JoaoMario109/ifsc-pi3-eletronic-load/docs/assets/eletronic-load.drawio.png

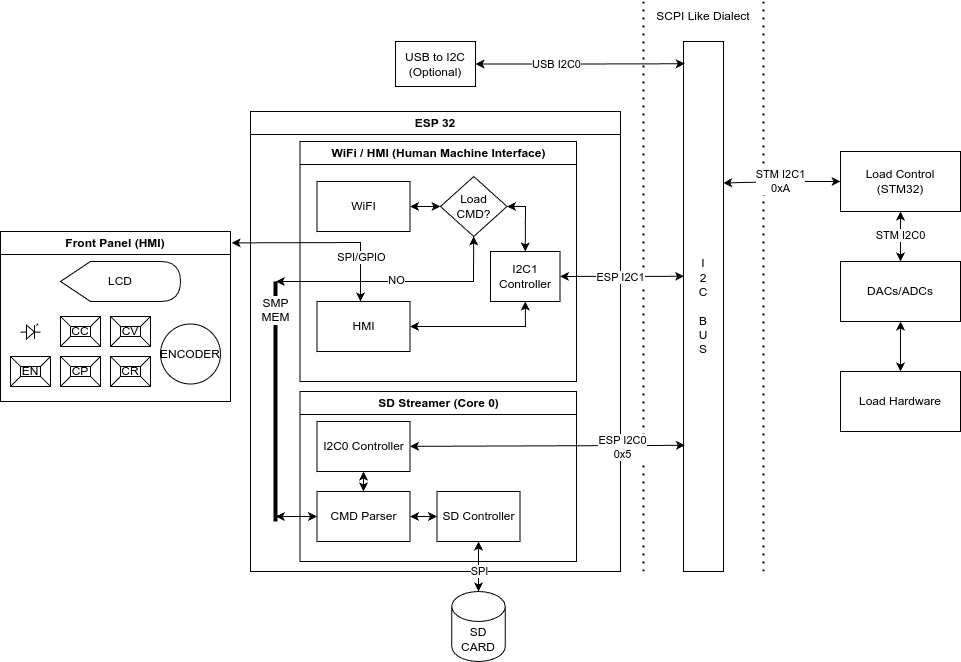
docs/assets/eletronic-load.drawio.png
