JoaoMario109/ifsc-pi3-eletronic-load/simulations/control/pid-hall.asc

C3: cap; 100n
C6: cap; 1n
D3: diode; LL4148
D4: diode; LL4148
D5: diode; LL4148
D6: diode; LL4148
DUT: voltage; PULSE(5 12 0 0p 0p 1m 2m)
Q1: npn
Q2: pnp; 2SB1375
Q3: npn
R1: res; 10
R2: res; 0.1
R3: res; 10
R4: res; 10
R5: res; 3.3k
R6: res; 3.3k
R7: res; 2.7k
R8: res; 3.3k
R9: res; 3.3k
R10: res; 720
R11: res; 1k
R13: res; 5k
R14: res; 3.30k
R15: res; 0.1
R16: res; 1k
U1: LM324_ST
U3: LM324_ST
U5: 
V1: voltage-; 12
V2: voltage; 1.65
V3: voltage-; PULSE(0 0.4 0 1p 1p 0.5m 1m)
V5: voltage-; 3.3
Named nets: vcc, 0, +3.3V, B2, B1, i_sensor, control_action, _control_action, setpoint
.tran 0 16m 2m startup
R10 -> reducing resistance increace velocity and ringing
C3 -> increase capacitance decrease rise time and increase ringing
C6 -> + capacitance = lower speed
