JoaoMario109/ifsc-pi3-eletronic-load/simulations/analog/voltage.asc

C1: cap; 1µ
C2: cap; 100n
C3: cap; 10n
C4: cap; 100n
D2: zener; BZX84B12VL
D3: zener; BZX84B12VL
D4: zener; PH_BZX585-B3V3
Q1: npn
R1: res; 10k
R2: res; 51k
R3: res; 10k
R4: res; 51k
R5: res; 50k
R6: res; 50k
R7: res; 1k
R8: res; 1k
R9: res; 1k
R10: res; 500
R11: res; 100
U2: LM324_ST
V1: voltage; 12
Vcm1: voltage; SINE(5 5 100 0 0 0); AC 50
Vcm: voltage; PULSE(0 10 0 0.01 0.01 0 0.02)
Vdut1: voltage; SINE(0 100 1 0 0 0 0); AC 100
Vdut: voltage; PULSE(0 100 0 1 1 0 2)
Vripple: voltage; SINE(0 6 1k)
Named nets: 0, Vcc, vout, Vdut-, Vdut+
;.ac dec 1k 1 10k
.tran 0 2 0
