JoaoMario109/ifsc-pi3-eletronic-load/firmware/load/Core/Inc/main.h

#define EXTERNAL_TRIGGER_OUT_Pin GPIO_PIN_13
#define EXTERNAL_TRIGGER_OUT_GPIO_Port GPIOC
#define EXTERNAL_TRIGGER_IN_Pin GPIO_PIN_14
#define EXTERNAL_TRIGGER_IN_GPIO_Port GPIOC
#define LED_RED_Pin GPIO_PIN_7
#define LED_RED_GPIO_Port GPIOA
#define LED_GREEN_Pin GPIO_PIN_0
#define LED_GREEN_GPIO_Port GPIOB
#define ADC_ALERT_Pin GPIO_PIN_1
#define ADC_ALERT_GPIO_Port GPIOB
#define ADC_ALERT_EXTI_IRQn EXTI1_IRQn
#define PERIPHERIAL_SCL_Pin GPIO_PIN_10
#define PERIPHERIAL_SCL_GPIO_Port GPIOB
#define PERIPHERIAL_SDA_Pin GPIO_PIN_11
#define PERIPHERIAL_SDA_GPIO_Port GPIOB
#define ENABLE_LOAD_Pin GPIO_PIN_15
#define ENABLE_LOAD_GPIO_Port GPIOB
#define FAN_Pin GPIO_PIN_8
#define FAN_GPIO_Port GPIOA
