JoaoMario109/ifsc-pi3-eletronic-load/firmware/hmi/main/peripherals/buttons.c

#include "driver/gpio.h"
#include "esp_attr.h"
#include "esp_timer.h"

#include "common.h"
#include "peripherals/buttons.h"
#include "utils.h"

/** Definitions */

#define MODULE_NAME "peripherals.buttons"

/** Handlers */
volatile bool h_pending_button_cc = false;
volatile bool h_pending_button_cv = false;
volatile bool h_pending_button_cr = false;
volatile bool h_pending_button_cp = false;
volatile bool h_pending_button_enc = false;

/** Enable is trick because of not being able to deal ok with IRQ */
bool h_button_en = false;
bool h_button_en_last = false;
bool h_button_en_rising = false;
bool h_button_en_falling = false;

/** We keep a ref for long press */
bool h_button_enc = false;
unsigned long h_button_enc_last = 0;
bool h_button_enc_long_press = false;

/** Forward Decl */
static void buttons_direction_init(void);
static void buttons_irq_init(void);
static void gpio_isr_handler(void *arg);

/**
 * @brief Set up default buttons configuration
 * @return void
 */
void buttons_init(void)
{
  LOG_PROLOG

  buttons_direction_init();
  buttons_irq_init();

  LOG_EPILOG
}

void button_en_update()
{
  h_button_en = gpio_get_level(GPIO_BTN_EN);
  h_button_en_rising = h_button_en && !h_button_en_last;
  h_button_en_falling = !h_button_en && h_button_en_last;
  h_button_en_last = h_button_en;
}

void button_enc_update()
{
  h_button_enc = !gpio_get_level(GPIO_ENCODER_BTN);

  /** Millis since start */
  unsigned long now = (unsigned long)(esp_timer_get_time() / 1000ULL);

  if (h_button_enc) {
    if (h_button_enc_last == 0) {
      h_button_enc_last = now;
    } else if ((now - h_button_enc_last) >= BTN_ENC_LONG_PRESS_MS) {
      h_button_enc_long_press = true;
    }
  } else {
    h_button_enc_last = 0;
    h_button_enc_long_press = false;
  }
}

/**
 * @brief Enable buttons interrupts allowing to detect button press
 * @return void
 */
void buttons_activate(void)
{
  LOG_PROLOG

  gpio_intr_enable(GPIO_BTN_CC);
  gpio_intr_enable(GPIO_BTN_CV);
  gpio_intr_enable(GPIO_BTN_CR);
  gpio_intr_enable(GPIO_BTN_CP);
  gpio_intr_enable(GPIO_ENCODER_BTN);

  LOG_EPILOG
}

/**
 * @brief Disable buttons interrupts
 * @return void
 */
void buttons_deactivate(void)
{
  LOG_PROLOG

  gpio_intr_disable(GPIO_BTN_CC);
  gpio_intr_disable(GPIO_BTN_CV);
  gpio_intr_disable(GPIO_BTN_CR);
  gpio_intr_disable(GPIO_BTN_CP);
  gpio_intr_disable(GPIO_ENCODER_BTN);

  LOG_EPILOG
}

/**
 * @brief Enable encoder button interrupt
 * @return void
 */
void button_enc_activate(void)
{
  gpio_intr_enable(GPIO_ENCODER_BTN);
}

/**
 * @brief Disable encoder button interrupt
 * @return void
 */
void button_enc_deactivate(void)
{
  gpio_intr_disable(GPIO_ENCODER_BTN);
}

/**
 * @brief Clear all pending IRQ
 * @return void
 */
void clear_all_pending_irq(void)
{
  h_pending_button_cc = false;
  h_pending_button_cv = false;
  h_pending_button_cr = false;
  h_pending_button_cp = false;
  h_pending_button_enc = false;
}

/** Implementations */
static void buttons_direction_init(void)
{
  LOG_PROLOG

  ESP_ERROR_CHECK(gpio_set_direction(GPIO_BTN_CC, GPIO_MODE_INPUT));
  ESP_ERROR_CHECK(gpio_set_direction(GPIO_BTN_CV, GPIO_MODE_INPUT));
  ESP_ERROR_CHECK(gpio_set_direction(GPIO_BTN_CR, GPIO_MODE_INPUT));
  ESP_ERROR_CHECK(gpio_set_direction(GPIO_BTN_CP, GPIO_MODE_INPUT));

  ESP_ERROR_CHECK(gpio_set_direction(GPIO_BTN_EN, GPIO_MODE_INPUT));
  ESP_ERROR_CHECK(gpio_set_pull_mode(GPIO_BTN_EN, GPIO_PULLUP_ONLY));

  ESP_ERROR_CHECK(gpio_set_direction(GPIO_ENCODER_BTN, GPIO_MODE_INPUT));
  ESP_ERROR_CHECK(gpio_set_pull_mode(GPIO_ENCODER_BTN, GPIO_PULLUP_ONLY));

  LOG_EPILOG
}

static void buttons_irq_init(void)
{
  LOG_PROLOG

  ESP_ERROR_CHECK(gpio_install_isr_service(0));

  ESP_ERROR_CHECK(gpio_set_intr_type(GPIO_BTN_CC, GPIO_INTR_POSEDGE));
  ESP_ERROR_CHECK(gpio_isr_handler_add(GPIO_BTN_CC, gpio_isr_handler, (void*)GPIO_BTN_CC));

  ESP_ERROR_CHECK(gpio_set_intr_type(GPIO_BTN_CV, GPIO_INTR_POSEDGE));
  ESP_ERROR_CHECK(gpio_isr_handler_add(GPIO_BTN_CV, gpio_isr_handler, (void*)GPIO_BTN_CV));

  ESP_ERROR_CHECK(gpio_set_intr_type(GPIO_BTN_CR, GPIO_INTR_POSEDGE));
  ESP_ERROR_CHECK(gpio_isr_handler_add(GPIO_BTN_CR, gpio_isr_handler, (void*)GPIO_BTN_CR));

  ESP_ERROR_CHECK(gpio_set_intr_type(GPIO_BTN_CP, GPIO_INTR_POSEDGE));
  ESP_ERROR_CHECK(gpio_isr_handler_add(GPIO_BTN_CP, gpio_isr_handler, (void*)GPIO_BTN_CP));

  ESP_ERROR_CHECK(gpio_set_intr_type(GPIO_ENCODER_BTN, GPIO_INTR_POSEDGE));
  ESP_ERROR_CHECK(gpio_isr_handler_add(GPIO_ENCODER_BTN, gpio_isr_handler, (void*)GPIO_ENCODER_BTN));

  LOG_EPILOG
}

/** Interrupt */
static void IRAM_ATTR gpio_isr_handler(void *arg)
{
  uint32_t gpio_num = (uint32_t)arg;

  switch (gpio_num)
  {
    case GPIO_BTN_CC:
      h_pending_button_cc = true;
      break;
    case GPIO_BTN_CV:
      h_pending_button_cv = true;
      break;
    case GPIO_BTN_CR:
      h_pending_button_cr = true;
      break;
    case GPIO_BTN_CP:
      h_pending_button_cp = true;
      break;
    case GPIO_ENCODER_BTN:
      h_pending_button_enc = true;
      break;
    default:
      break;
  }
}
